is-watering/isw_seaslug/firmware/qmk/src/keymaps/via_az1uball/config.h

// Copyright 2023 is_watering (@is_watering)
// SPDX-License-Identifier: GPL-2.0-or-later

#pragma once

#define DYNAMIC_KEYMAP_LAYER_COUNT 4
#define PIMORONI_TRACKBALL_SCALE 6
#define POINTING_DEVICE_TASK_THROTTLE_MS 10
#define POINTING_DEVICE_ROTATION_180
